Safecast/safepulse/Kicad files/OpenHVPS-5/SafePulse_back.jpg

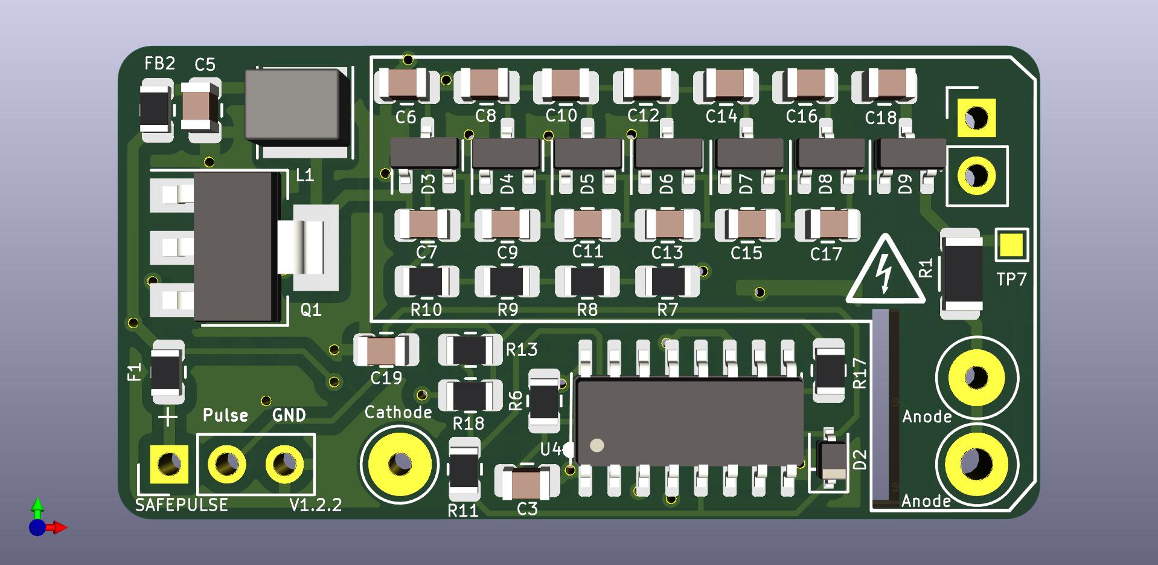
Kicad files/OpenHVPS-5/SafePulse_back.jpg
